AnasSarkiz/Game-Boy-Enhance/docs/previews/audio.png

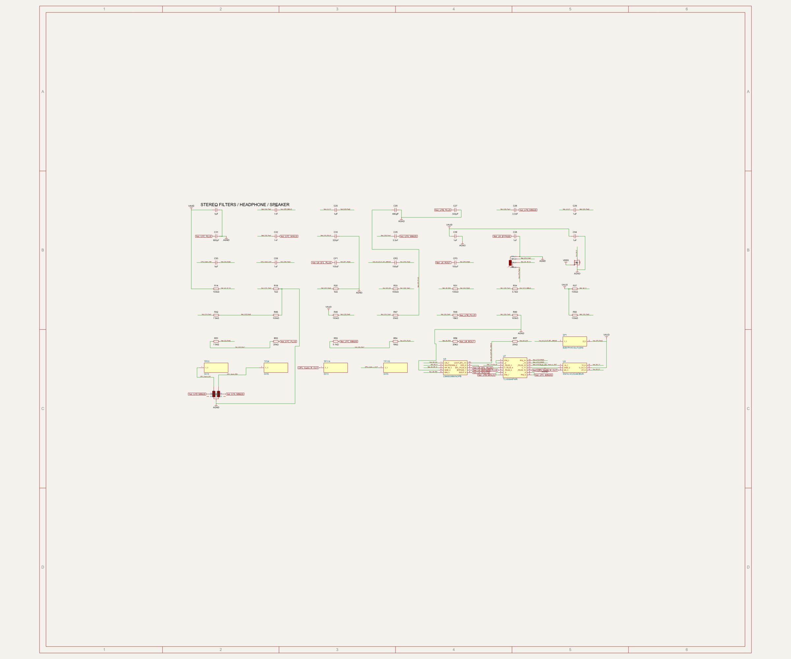
docs/previews/audio.png
